swehner/foos/doc/screenshot.jpg

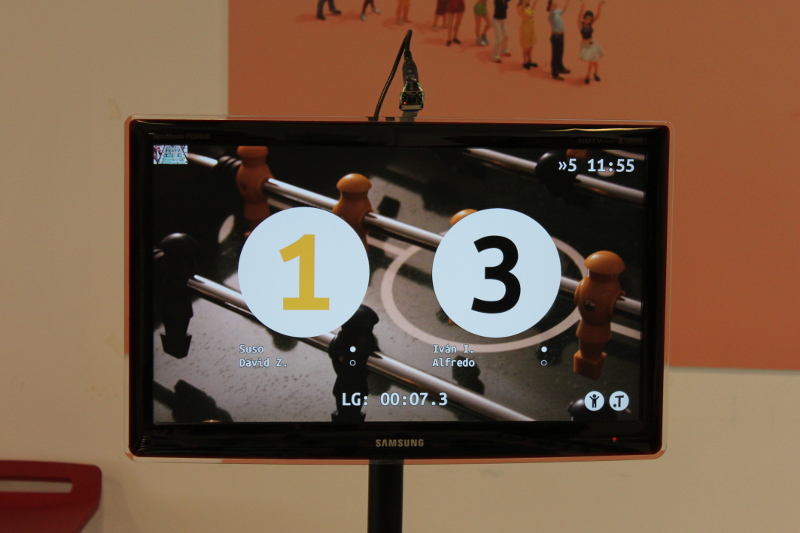
doc/screenshot.jpg
