swehner/foos/img/bg/cc1.jpg

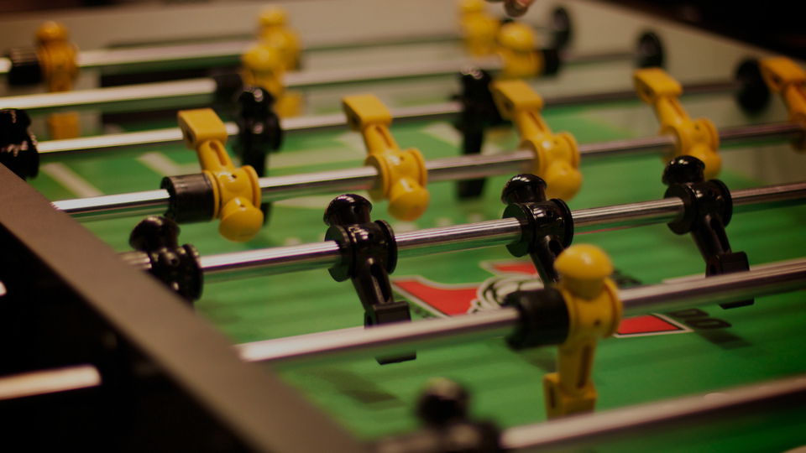
img/bg/cc1.jpg
