swehner/foos/img/bg/cc2.jpg

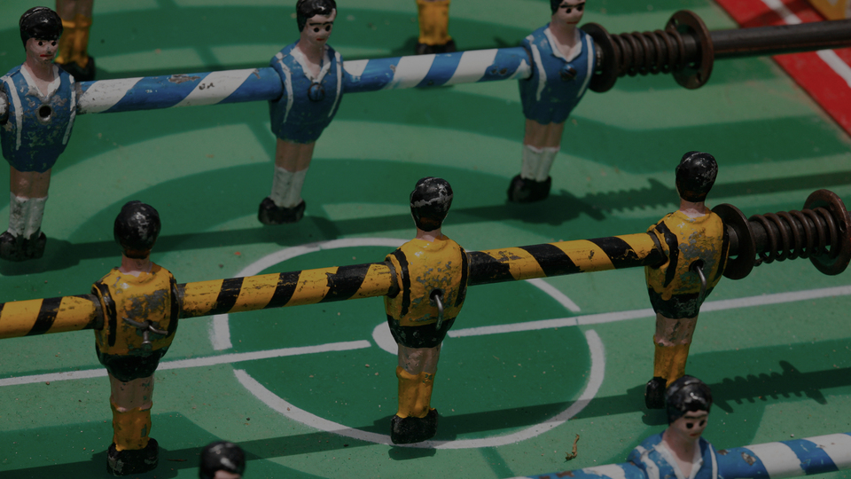
img/bg/cc2.jpg
