swehner/foos/img/bg/cc3.jpg

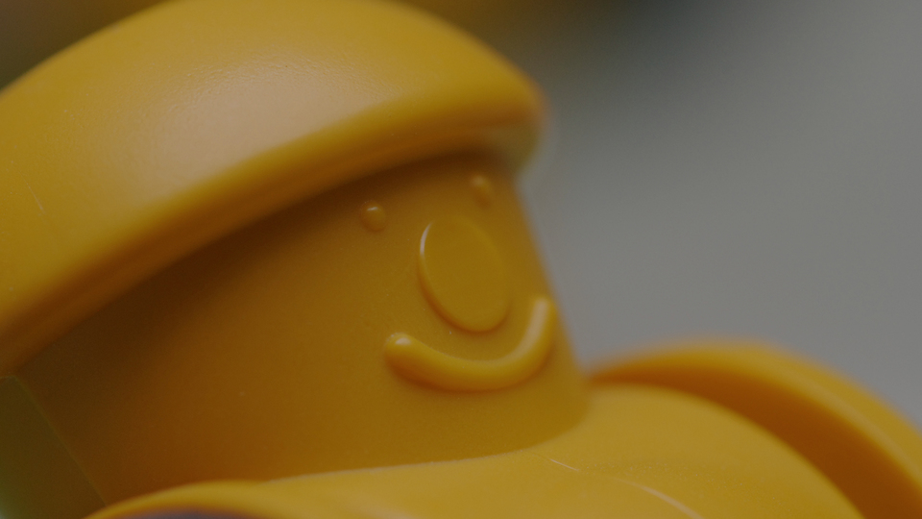
img/bg/cc3.jpg
