swehner/foos/img/bg/cc5.jpg

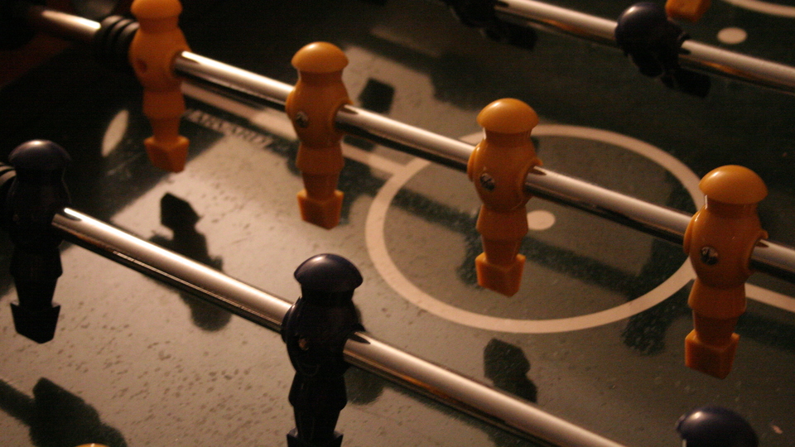
img/bg/cc5.jpg
