swehner/foos/img/bg/cc7.jpg

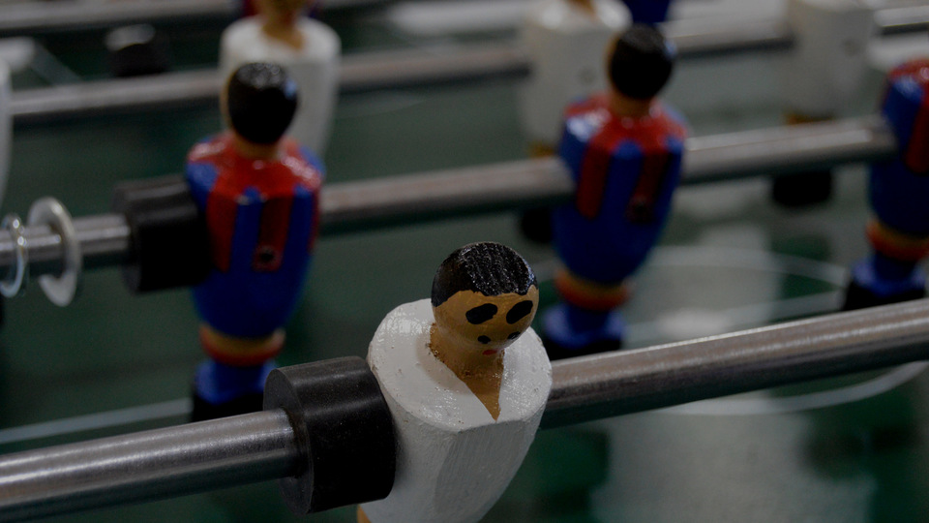
img/bg/cc7.jpg
