swehner/foos/img/bg/DSC00086.jpg

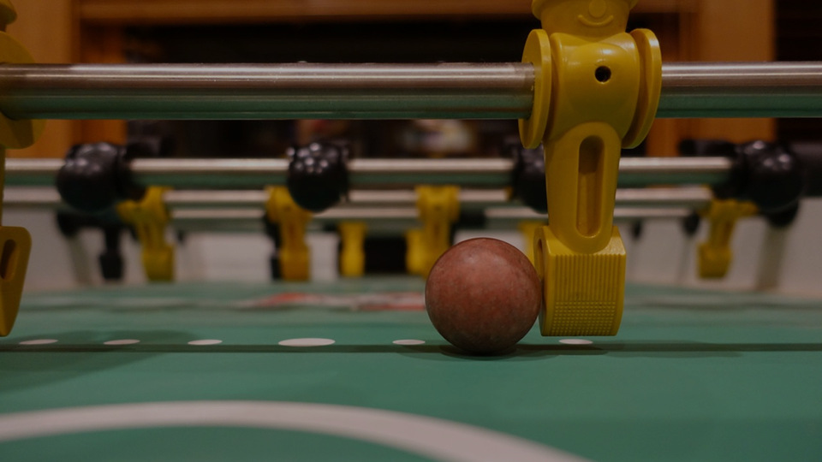
img/bg/DSC00086.jpg
