swehner/foos/img/bg/foosball.jpg

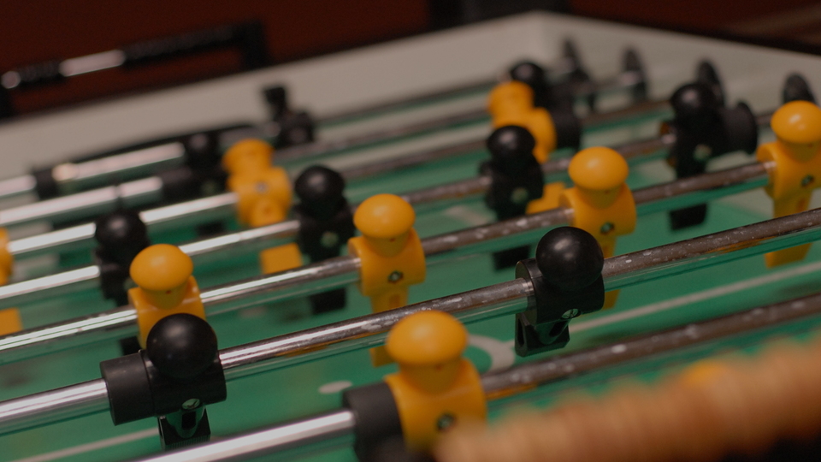
img/bg/foosball.jpg
