swehner/foos/img/numbers/0.png

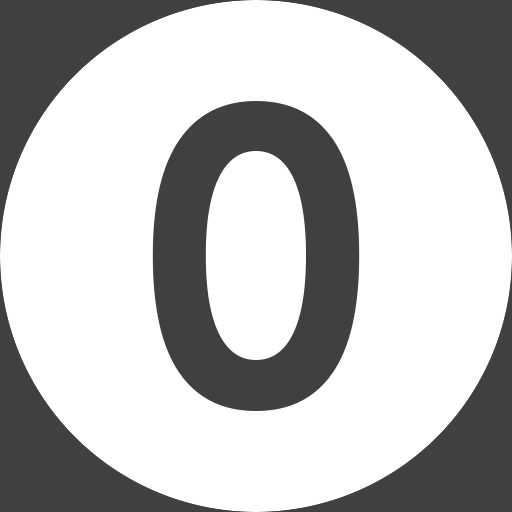
img/numbers/0.png
