swehner/foos/img/numbers/1.png

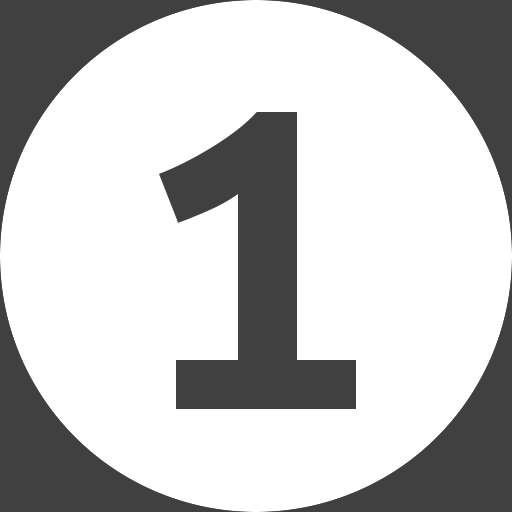
img/numbers/1.png
