swehner/foos/img/numbers/2.png

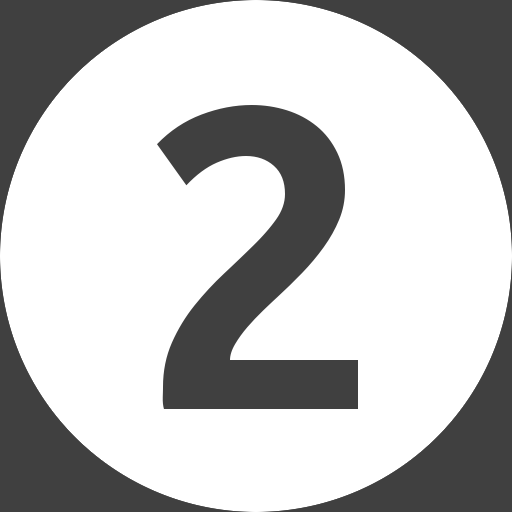
img/numbers/2.png
