swehner/foos/img/numbers/3.png

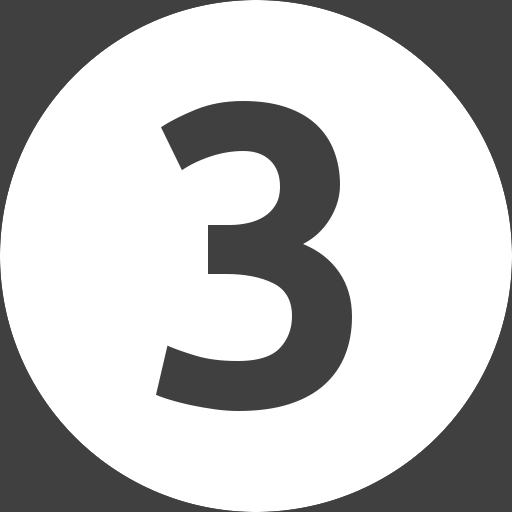
img/numbers/3.png
