swehner/foos/img/numbers/4.png

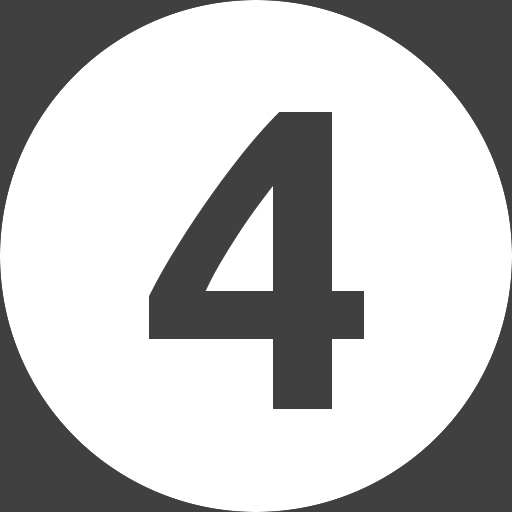
img/numbers/4.png
