swehner/foos/img/numbers/5.png

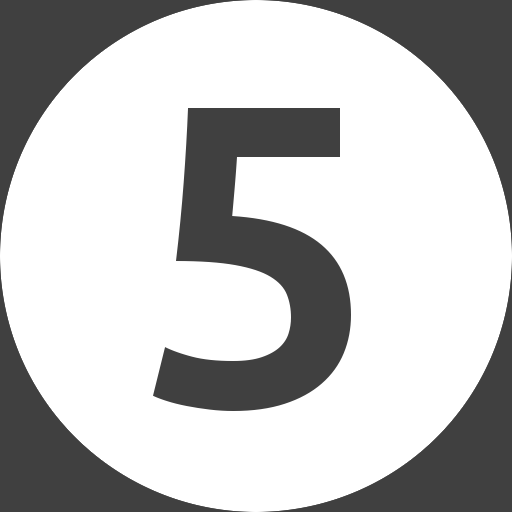
img/numbers/5.png
