swehner/foos/img/numbers/6.png

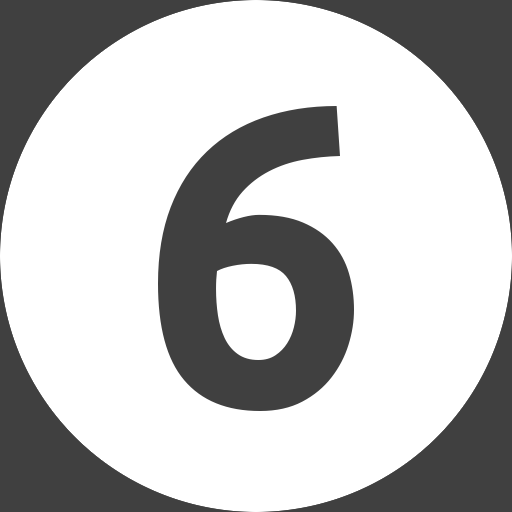
img/numbers/6.png
