swehner/foos/img/numbers/7.png

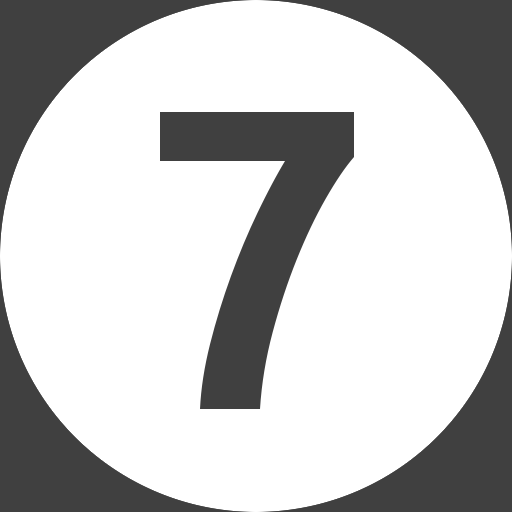
img/numbers/7.png
