swehner/foos/img/numbers/9.png

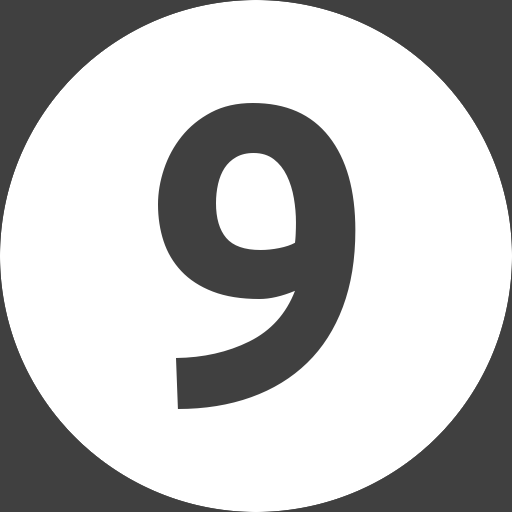
img/numbers/9.png
