swehner/foos/img/numbers/10.png

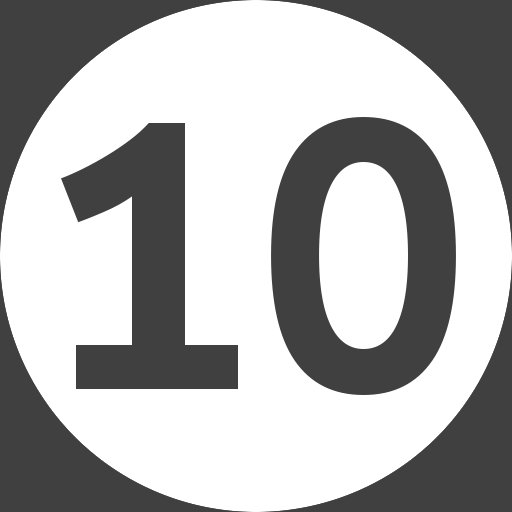
img/numbers/10.png
