swehner/foos/img/numbers/circle_m.png

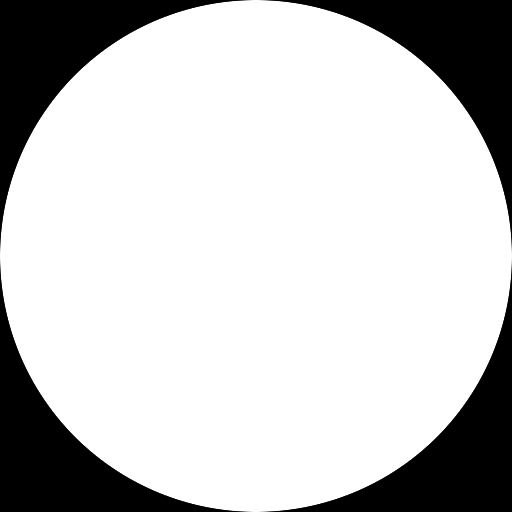
img/numbers/circle_m.png
