swehner/foos/config_base.py

# basic set of plugins
plugins = set(['score', 'game', 'sound', 'io_debug', 'menu', 'control', 'league', 'leds', 'io_evdev_keyboard'])

onscreen_leds_enabled = False
blank_console = True
standby_timeout_secs = 600
bg_change_secs = 300
# use dispmanx to draw bg as a separate layer
draw_bg_with_dispmanx = True

clock_format = "%H:%M"

hipchat_token = 'your_token'
hipchat_room = 'your_room_id'

min_goal_usecs = 1000
min_secs_between_goals = 3

show_instructions = True

team_names = {"yellow": "yellow", "black": "black"}
team_colors = {"yellow": (1, 0.7, 0), "black": (0, 0, 0)}

# game modes: tuples of (winning score, timeout in minutes)
game_modes = [(None, None), (3, None), (5, None), (3, 120)]

replay_path = '/dev/shm/replay'
replay_fps = 25
ignore_recent_chunks = 1
short_chunks = 10
long_chunks = 25

league_dir = './league'
league_url = 'http://localhost:8888/api'
league_apikey = 'put-your-apikey-here'

video_size=(1280, 720)
video_fps = 49
camera_preview = "-p 0,0,128,72"
camera_chunk_settings = "-sg 100 -wr 100 -g 10"
camera_extra_params = "--ev 7"


# config parameters for motion detector
# MV frame size
md_size = (video_size[0] // 16 + 1, video_size[1] // 16)
# crop pixels on each size of the frame to avoid detecting movement outside of the table
md_crop_x = 25
# threshold to consider MV movement
md_mv_threshold = 100000
# number of vectors to consider frame to contain movement
md_min_vectors = 30
# number of contiguous frames to required to consider it movemen
md_min_frames = 9

# send people_stop_playing event after X seconds without movement
md_ev_absence_timeout = 30
# send movement_detected every X seconds
md_ev_interval = 2

log = {
    "version": 1,
    "disable_existing_loggers": False,
    "formatters": {
        "simple": {
            "format": "%(asctime)s %(levelname)7s %(name)s - %(message)s",
            "datefmt": "%H:%M:%S"
        },
        "console": {
            "format": "%(levelname)7s - %(message)s"
        }
    },

    "handlers": {
        "console": {
            "class": "logging.StreamHandler",
            "level": "DEBUG",
            "formatter": "console",
            "stream": "ext://sys.stdout"
        },

        "file_handler": {
            "class": "logging.handlers.RotatingFileHandler",
            "level": "DEBUG",
            "formatter": "simple",
            "filename": "/dev/shm/foos_event.log",
            "maxBytes": 1000000,
            "backupCount": 3
        },
    },

    "loggers": {
        "plugins.event_debugger": {
            "level": "DEBUG",
            "handlers": ["file_handler"],
            "propagate": "no",
        },
        "pi3d": {
            "level": "WARN",
            "handlers": ["console", "file_handler"],
            "propagate": "no",
        }

    },
    "root": {
        "level": "INFO",
        "handlers": ["console", "file_handler"]
    }
}
